mindingulove/pico-w5500-ups/ups_secrets.example.h

#pragma once

// Copy this file to ups_secrets.h and replace every placeholder locally.
// ups_secrets.h is intentionally excluded from Git.
#define UPS_OTA_TOKEN "replace_with_a_long_random_token"
#define UPS_CALIBRATION_TOKEN "replace_with_a_different_long_random_token"
#define UPS_MQTT_USER ""
#define UPS_MQTT_PASSWORD ""
